eggsworks/tamago60/tamago60/tamago60.kicad_sch

## KiCad design tamago60/tamago60.kicad_sch (2023-04-23)

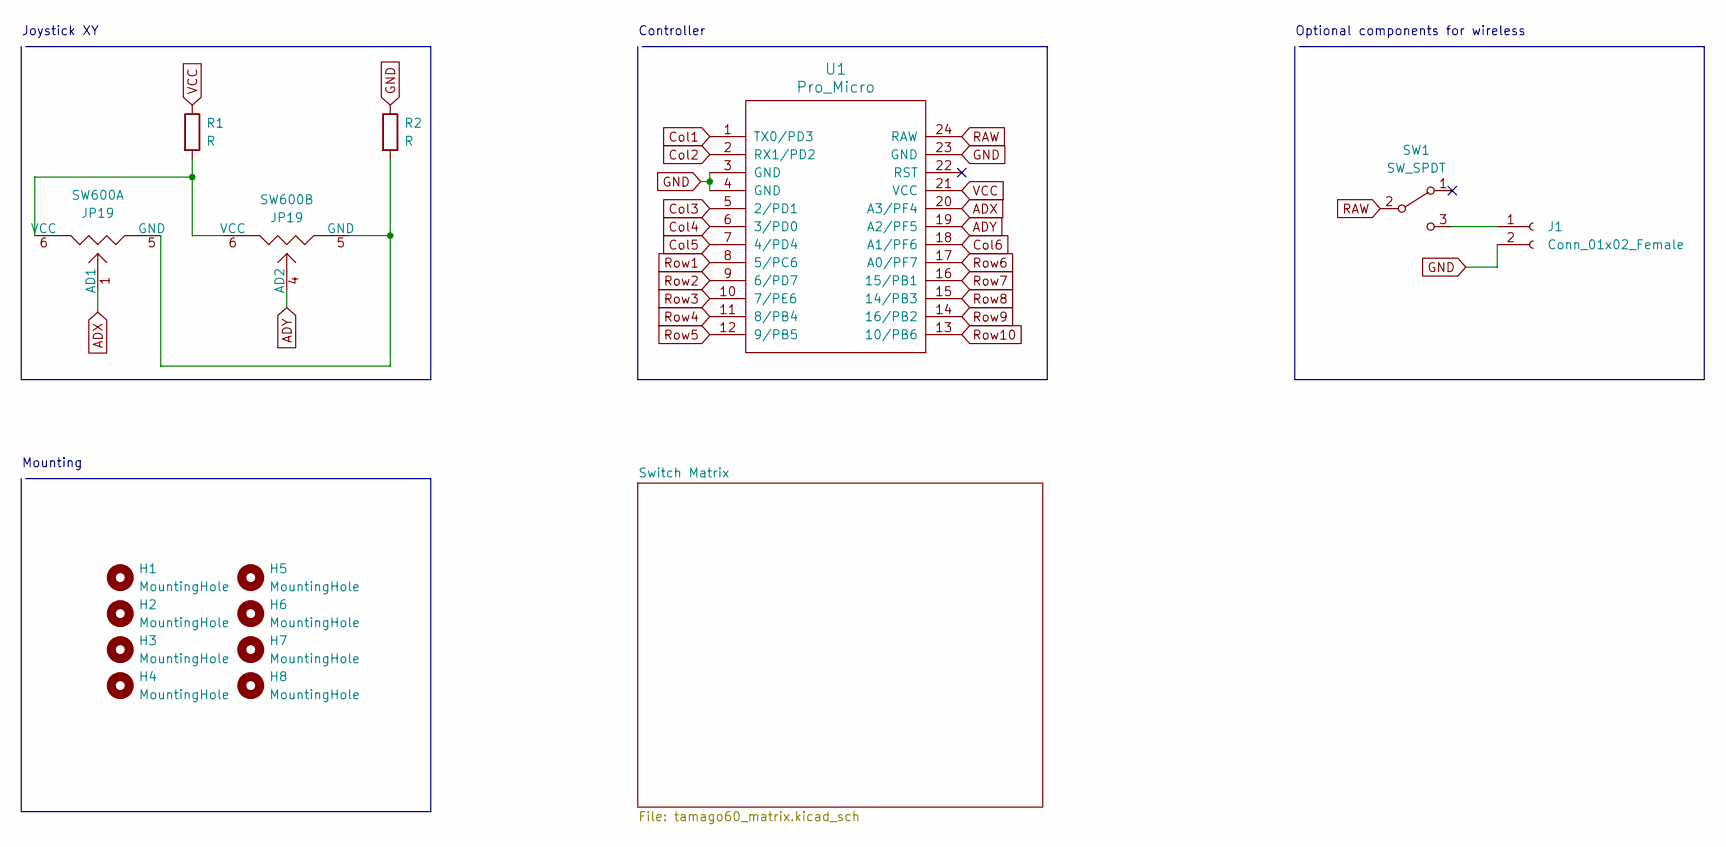
[picture p4: schematic tamago60.kicad_sch]

Parts:
H1, H2, H3, H4, H5, H6, H7, H8: MountingHole; MountingHole_2.2mm_M2
J1: Conn_01x02_Female; JST_PH_S2B-PH-K_1x02_P2.00mm_Horizontal
R1, R2: R; R_1206_3216Metric
SW1: SW_SPDT; SW_SPDT_PCM12
SW600: JP19
U1: Pro_Micro; ProMicro

Connections:
ADX: SW600.1 (AD1), U1.20 (A3/PF4)
ADY: SW600.4 (AD2), U1.19 (A2/PF5)
Col1: U1.1 (TX0/PD3)
Col2: U1.2 (RX1/PD2)
Col3: U1.5 (2/PD1)
Col4: U1.6 (3/PD0)
Col5: U1.7 (4/PD4)
Col6: U1.18 (A1/PF6)
GND: J1.2, R2.1, U1.3 (GND), U1.4 (GND), U1.23 (GND)
unnamed: J1.1, SW1.3 (C)
unnamed: R1.2, SW600.6 (VCC)
unnamed: R2.2, SW600.5 (GND)
RAW: SW1.2 (B), U1.24 (RAW)
Row1: U1.8 (5/PC6)
Row2: U1.9 (6/PD7)
Row3: U1.10 (7/PE6)
Row4: U1.11 (8/PB4)
Row5: U1.12 (9/PB5)
Row6: U1.17 (A0/PF7)
Row7: U1.16 (15/PB1)
Row8: U1.15 (14/PB3)
Row9: U1.14 (16/PB2)
Row10: U1.13 (10/PB6)
VCC: R1.1, U1.21 (VCC)

Notes on the sheet:
Mounting
Optional components for wireless
Controller
Joystick XY
