eggsworks/tamago60/tamago60/tamago60_matrix.kicad_sch

## KiCad design tamago60/tamago60_matrix.kicad_sch (2023-04-23)

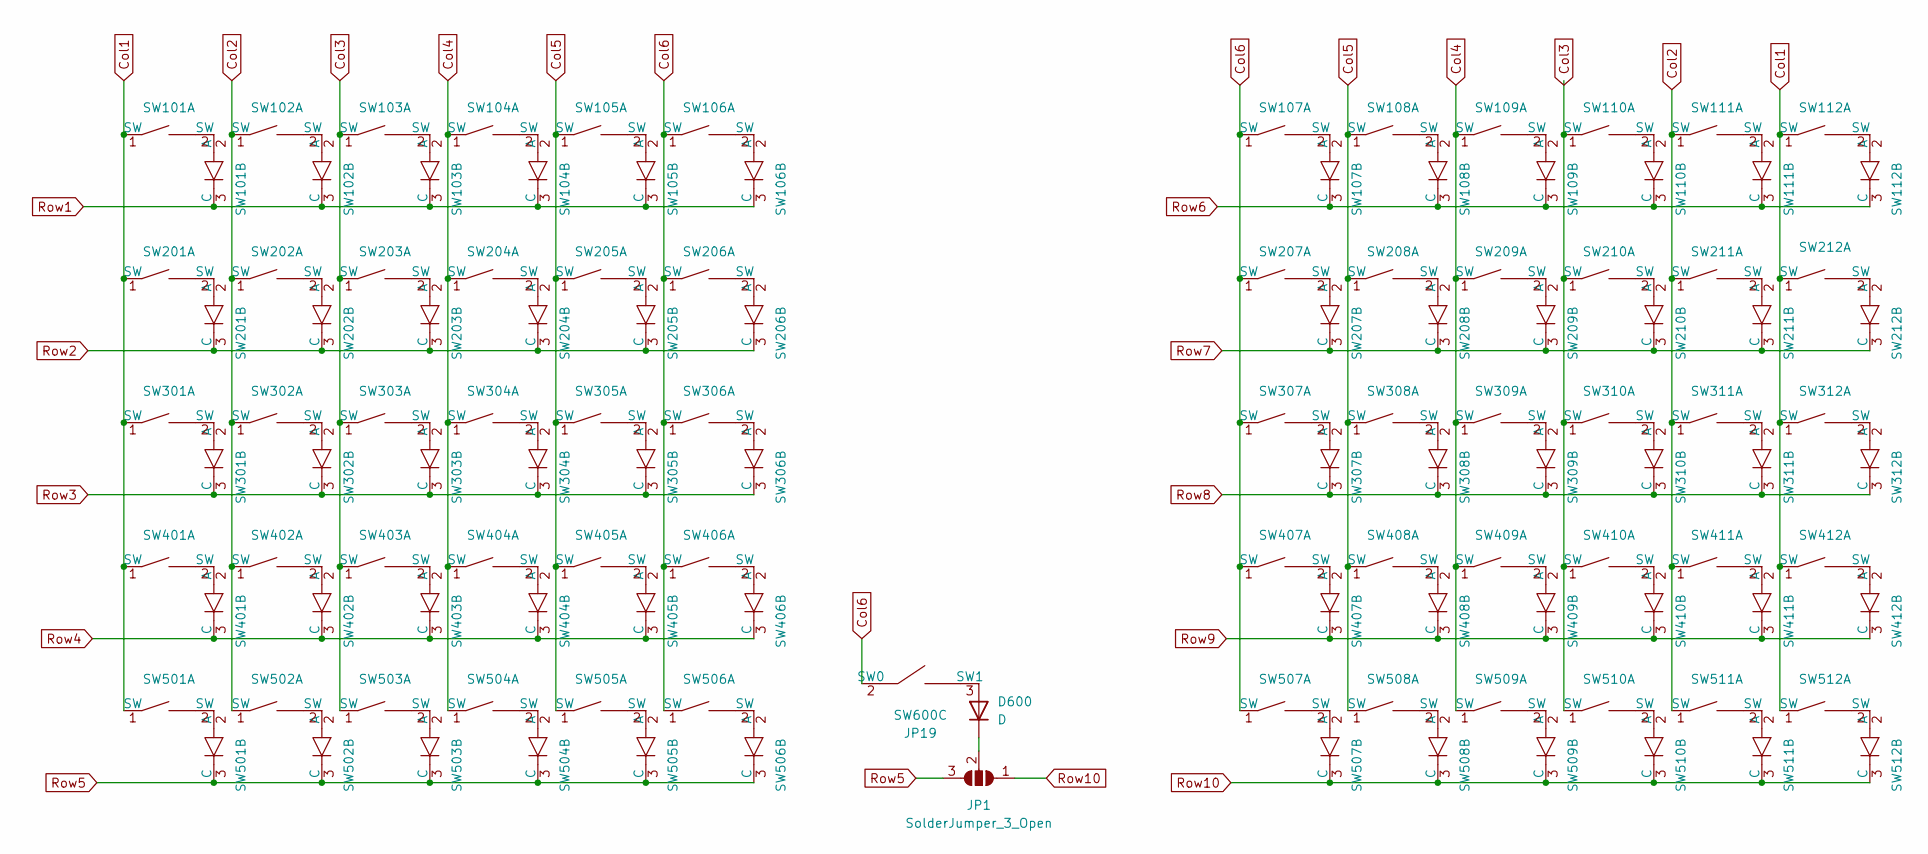
[picture p5: schematic tamago60_matrix.kicad_sch]

Parts:
D600: D; D_SOD-123
JP1: SolderJumper_3_Open; SolderJumper-3_P1.3mm_Open_Pad1.0x1.5mm_NumberLabels
SW101, SW102, SW103, SW104, SW105, SW106, SW107, SW108, SW109, SW110, SW111, SW112, SW201, SW202, SW203, SW204, SW205, SW206, SW207, SW208, SW209, SW210, SW211, SW212, SW301, SW302, SW303, SW304, SW305, SW306, SW307, SW308, SW309, SW310, SW311, SW312, SW401, SW402, SW403, SW404, SW405, SW406, SW407, SW408, SW409, SW410, SW411, SW412, SW501, SW502, SW503, SW504, SW506, SW507, SW509, SW510, SW511, SW512: switch_with_diode; Choc_Hotswap
SW505: switch_with_diode; Choc_Hotswap_2u_left
SW508: switch_with_diode; Choc_Hotswap_2u_right
SW600: JP19

Connections:
Col1: SW101.1 (SW), SW112.1 (SW), SW201.1 (SW), SW212.1 (SW), SW301.1 (SW), SW312.1 (SW), SW401.1 (SW), SW412.1 (SW), SW501.1 (SW), SW512.1 (SW)
Col2: SW102.1 (SW), SW111.1 (SW), SW202.1 (SW), SW211.1 (SW), SW302.1 (SW), SW311.1 (SW), SW402.1 (SW), SW411.1 (SW), SW502.1 (SW), SW511.1 (SW)
Col3: SW103.1 (SW), SW110.1 (SW), SW203.1 (SW), SW210.1 (SW), SW303.1 (SW), SW310.1 (SW), SW403.1 (SW), SW410.1 (SW), SW503.1 (SW), SW510.1 (SW)
Col4: SW104.1 (SW), SW109.1 (SW), SW204.1 (SW), SW209.1 (SW), SW304.1 (SW), SW309.1 (SW), SW404.1 (SW), SW409.1 (SW), SW504.1 (SW), SW509.1 (SW)
Col5: SW105.1 (SW), SW108.1 (SW), SW205.1 (SW), SW208.1 (SW), SW305.1 (SW), SW308.1 (SW), SW405.1 (SW), SW408.1 (SW), SW505.1 (SW), SW508.1 (SW)
Col6: SW106.1 (SW), SW107.1 (SW), SW206.1 (SW), SW207.1 (SW), SW306.1 (SW), SW307.1 (SW), SW406.1 (SW), SW407.1 (SW), SW506.1 (SW), SW507.1 (SW), SW600.2 (SW0)
unnamed: D600.1 (K), JP1.2 (C)
unnamed: D600.2 (A), SW600.3 (SW1)
Row1: SW101.3 (C), SW102.3 (C), SW103.3 (C), SW104.3 (C), SW105.3 (C), SW106.3 (C)
Row2: SW201.3 (C), SW202.3 (C), SW203.3 (C), SW204.3 (C), SW205.3 (C), SW206.3 (C)
Row3: SW301.3 (C), SW302.3 (C), SW303.3 (C), SW304.3 (C), SW305.3 (C), SW306.3 (C)
Row4: SW401.3 (C), SW402.3 (C), SW403.3 (C), SW404.3 (C), SW405.3 (C), SW406.3 (C)
Row5: JP1.3 (B), SW501.3 (C), SW502.3 (C), SW503.3 (C), SW504.3 (C), SW505.3 (C), SW506.3 (C)
Row6: SW107.3 (C), SW108.3 (C), SW109.3 (C), SW110.3 (C), SW111.3 (C), SW112.3 (C)
Row7: SW207.3 (C), SW208.3 (C), SW209.3 (C), SW210.3 (C), SW211.3 (C), SW212.3 (C)
Row8: SW307.3 (C), SW308.3 (C), SW309.3 (C), SW310.3 (C), SW311.3 (C), SW312.3 (C)
Row9: SW407.3 (C), SW408.3 (C), SW409.3 (C), SW410.3 (C), SW411.3 (C), SW412.3 (C)
Row10: JP1.1 (A), SW507.3 (C), SW508.3 (C), SW509.3 (C), SW510.3 (C), SW511.3 (C), SW512.3 (C)
